savagesmc/bandpass_filter/models/uhf_filter_9th.spice

UHF Bandpass Filter - 9th Order Chebyshev

V1 SRC 0 DC 0 AC 1 PULSE( 0 5 1u 1u 1u 1 1)
R1 SRC IN 50

C1 IN 0 4.7p
L1 IN 0 22n

C2 IN N2 6.8p
L2 N2 N3 15n

C3 N3 0 8.2p
L3 N3 0 12n

C4 N3 N4 5.6p
L4 N4 N5 15n

C5 N5 0 8.2p
L5 N5 0 12n

C6 N5 N6 5.6p
L6 N6 N7 15n

C7 N7 0 8.2p
L7 N7 0 12n

C8 N7 N8 6.8p
L8 N8 OUT 15n

C9 OUT 0 4.7p
L9 OUT 0 22n
R2 OUT 0 50

.control
   let mc_runs = 1000
   let run = 1
   set curplot = new
   set scratch = $curplot

* 5% Tolerance
   set tol = 0.05

   define unif(nom, var) (nom + nom*var * sunif(0))

   dowhile run <= mc_runs

      alter C1 = unif(4.7p, $tol)
      alter L1 = unif(22n, $tol)

      alter C2 = unif(6.8p, $tol)
      alter L2 = unif(15n, $tol)

      alter C3 = unif(8.2p, $tol)
      alter L3 = unif(12n, $tol)

      alter C4 = unif(5.6p, $tol)
      alter L4 = unif(15n, $tol)

      alter C5 = unif(8.2p, $tol)
      alter L5 = unif(12n, $tol)

      alter C6 = unif(5.6p, $tol)
      alter L6 = unif(15n, $tol)

      alter C7 = unif(8.2p, $tol)
      alter L7 = unif(12n, $tol)

      alter C8 = unif(6.8p, $tol)
      alter L8 = unif(15n, $tol)

      alter C9 = unif(4.7p, $tol)
      alter L9 = unif(22n, $tol)

      ac oct 100 100e6 1500e6

      set run ="$&run"
      set dt = $curplot
      setplot $scratch

      let loss{$run}={$dt}.v(out)/{$dt}.v(in)
      setplot $dt
      let run = run + 1
   end
   set nolegend
   hardcopy uhf_filter_9th_5tol.ps db({$scratch}.all) xlimit 100e6 1200e6 ylimit -55 5 ylabel 'UHF BPF - insertion loss'
   * plot db({$scratch}.all) xlimit 100e6 1200e6 ylimit -55 5 ylabel 'UHF BPF - insertion loss'
.endc
.end
